GaragemHacker/senseiot/sense1.0/hello_led/esp8266_esp_01_ftdi_logic_level_converter__bb.png

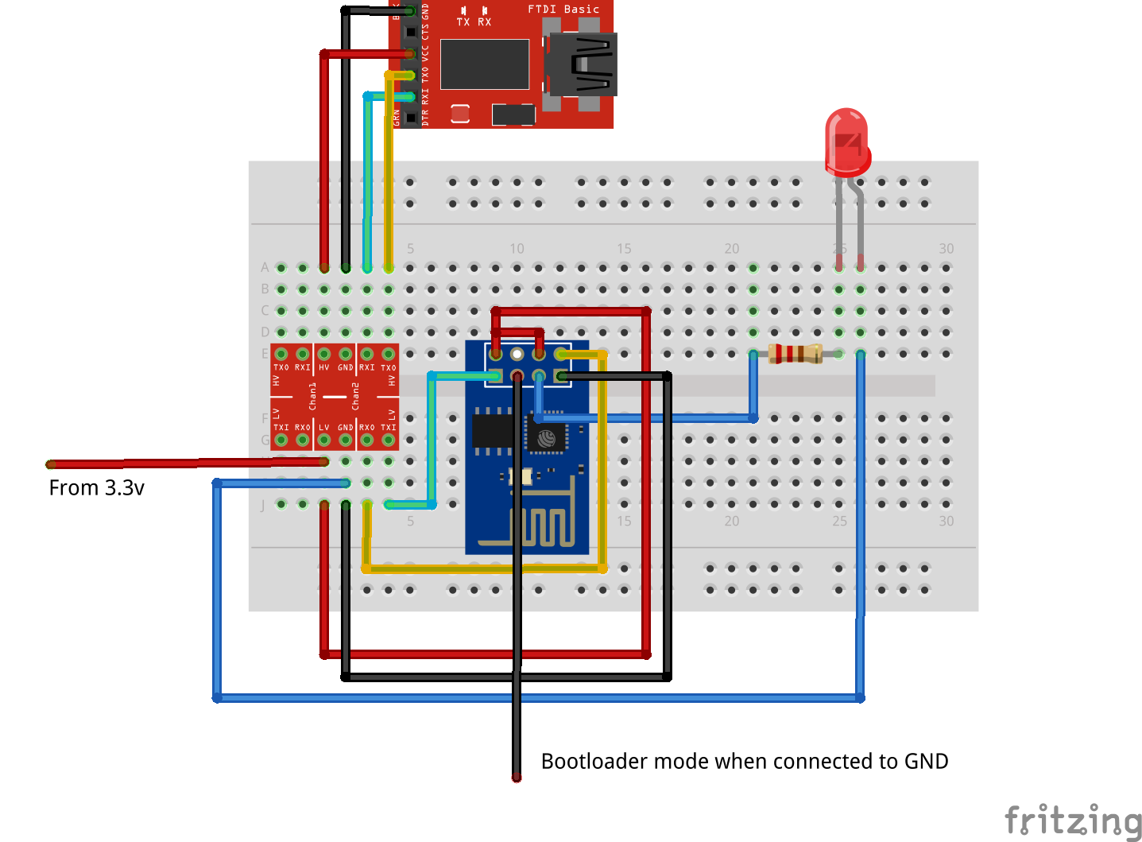
sense1.0/hello_led/esp8266_esp_01_ftdi_logic_level_converter__bb.png
