GaragemHacker/senseiot/sense1.0/ht/esp8266_esp_01_ftdi_logic_level_converter_dht11_bb.png

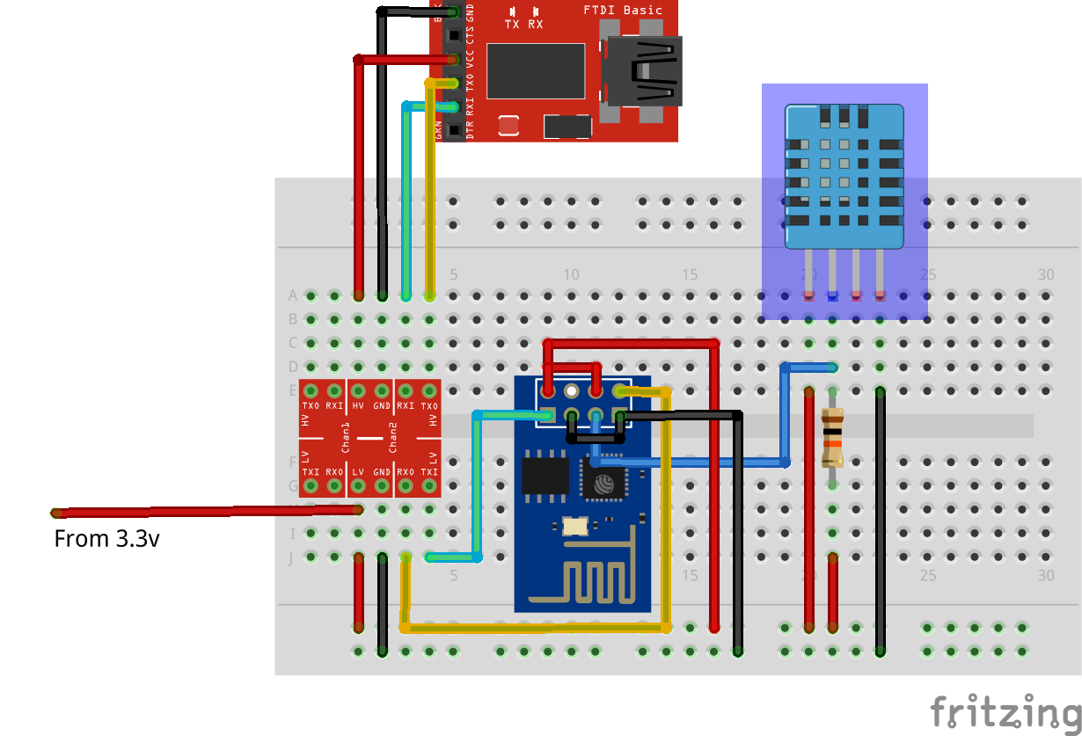
sense1.0/ht/esp8266_esp_01_ftdi_logic_level_converter_dht11_bb.png
