GaragemHacker/senseiot/sense2.0/ESP8266/Reles_mqtt/Reles_mqtt.ino

/*

 It connects to an MQTT server then:
  - on 0 switches off relay
  - on 1 switches on relay
  - on 2 switches the state of the relay

  - sends 0 on off relay
  - sends 1 on on relay

 It will reconnect to the server if the connection is lost using a blocking
 reconnect function. See the 'mqtt_reconnect_nonblocking' example for how to
 achieve the same result without blocking the main loop.

 The current state is stored in EEPROM and restored on bootup

*/

#include <ESP8266WiFi.h>
#include <PubSubClient.h>
#include <Bounce2.h>
#include <EEPROM.h>
#include <Stream.h>
#include "string.h"
#include <ESP8266mDNS.h>
#include <WiFiUdp.h>
#include <ArduinoOTA.h>

#define ESP8266_LED1 0  // D3
#define ESP8266_LED2 14 // D5

const char* ssid          = "";  
const char* password      = "";      
const char* mqtt_server   = "";
int port_server           = 1883;
const char* topicButton2  = "cmd/node1/rele1";
const char* topicButton3  = "cmd/node1/rele2";
//const char* outTopic    = "clients/cmd";
const char* outTopic      = "clients";

char ButtonChar[5];
char PayloadChar[5];
char clearChar[5];

String AnalogValue;
String TempValue;
String HumValue;
String Button;
String PayloadString;

WiFiClient ESP8266Client2;
PubSubClient client(ESP8266Client2);

long lastMsg = 0;
char msg[50];
int value = 0;
long now = 0;

void setup_wifi() {

  delay(10);
  // We start by connecting to a WiFi network
  Serial.println();
  Serial.print("Connecting to ");
  Serial.println(ssid);

  WiFi.begin(ssid, password);

  while (WiFi.status() != WL_CONNECTED) {
    delay(500);
    Serial.print(".");
  }
  
  Serial.println("");
  Serial.println("WiFi connected");
  Serial.println("IP address: ");
  Serial.println(WiFi.localIP());

  // Configuração do OTA  
  // Port defaults to 8266
  ArduinoOTA.setPort(8266);

  // Hostname defaults to esp8266-[ChipID]
  ArduinoOTA.setHostname("Node1-Reles");

  // No authentication by default
  ArduinoOTA.setPassword((const char *)"esp8266");

  ArduinoOTA.onStart([]() {
    Serial.println("Start");
  });
  ArduinoOTA.onEnd([]() {
    Serial.println("\nEnd");
  });
  ArduinoOTA.onProgress([](unsigned int progress, unsigned int total) {
    Serial.printf("Progress: %u%%\r", (progress / (total / 100)));
  });
  ArduinoOTA.onError([](ota_error_t error) {
    Serial.printf("Error[%u]: ", error);
    if (error == OTA_AUTH_ERROR) Serial.println("Auth Failed");
    else if (error == OTA_BEGIN_ERROR) Serial.println("Begin Failed");
    else if (error == OTA_CONNECT_ERROR) Serial.println("Connect Failed");
    else if (error == OTA_RECEIVE_ERROR) Serial.println("Receive Failed");
    else if (error == OTA_END_ERROR) Serial.println("End Failed");
  });
  ArduinoOTA.begin();
  Serial.println("Ready");
  Serial.print("IP address: ");
  Serial.println(WiFi.localIP());
  
}

void callback(char* topic, byte* payload, unsigned int length) {

  // Clear PayloadChar
  //PayloadChar = ";
  memcpy(PayloadChar, clearChar, 5);
  
  // Convert payload to String
  PayloadString = String((char*)payload);
  // Convert String to CharArray
  PayloadString.toCharArray(PayloadChar, 5);

  // LED 1
  if (strcmp(topic,topicButton2) == 0) {
      //Serial.print("1");

      Serial.println(PayloadChar); 

      if ( strcmp(PayloadChar,"desl") == 0){

        Serial.println(PayloadChar); 
        digitalWrite(ESP8266_LED1, LOW);
         
      }else if ( strcmp(PayloadChar,"liga") == 0){

        Serial.println(PayloadChar); 
        digitalWrite(ESP8266_LED1, HIGH);
        
      }
  }

  // LED 2
  if (strcmp(topic,topicButton3) == 0) {
      //Serial.print("1");

      Serial.println(PayloadChar); 

      if ( strcmp(PayloadChar,"desl") == 0){

        Serial.println(PayloadChar); 
        digitalWrite(ESP8266_LED2, LOW);
         
      }else if ( strcmp(PayloadChar,"liga") == 0){

        Serial.println(PayloadChar); 
        digitalWrite(ESP8266_LED2, HIGH);
        
      }
  }

  yield();
  
}

void reconnect() {
  // Loop until we're reconnected
  while (!client.connected()) {
    Serial.print("Attempting MQTT connection...");
    // Attempt to connect
    if (client.connect("ESP8266Client2")) {
      Serial.println("connected");
      // Once connected, publish an announcement...
      client.publish(outTopic, "Node2 Connected");
      // ... and resubscribe
      client.subscribe(topicButton2);
      client.subscribe(topicButton3);
      
    } else {
      Serial.print("failed, rc=");
      Serial.print(client.state());
      Serial.println(" try again in 5 seconds");
      // Wait 5 seconds before retrying
      delay(5000);
     }
   }
 }




void setup() {

  //Config Pin
  pinMode(ESP8266_LED1, OUTPUT);
  pinMode(ESP8266_LED2, OUTPUT);
  
  Serial.begin(115200);
  //establishContact();  // send a byte to establish contact until receiver responds
  setup_wifi();        // Connect to wifi 
  client.setServer(mqtt_server, port_server);
  client.setCallback(callback);
}

void loop() {
  
  // Verificação OTA update
  ArduinoOTA.handle();
    
  if (!client.connected()) {
    reconnect();
    yield();
  }
  
  client.loop();

}
